jaromir-sukuba/rsyn/media/IMG_20230515_151459656.jpg

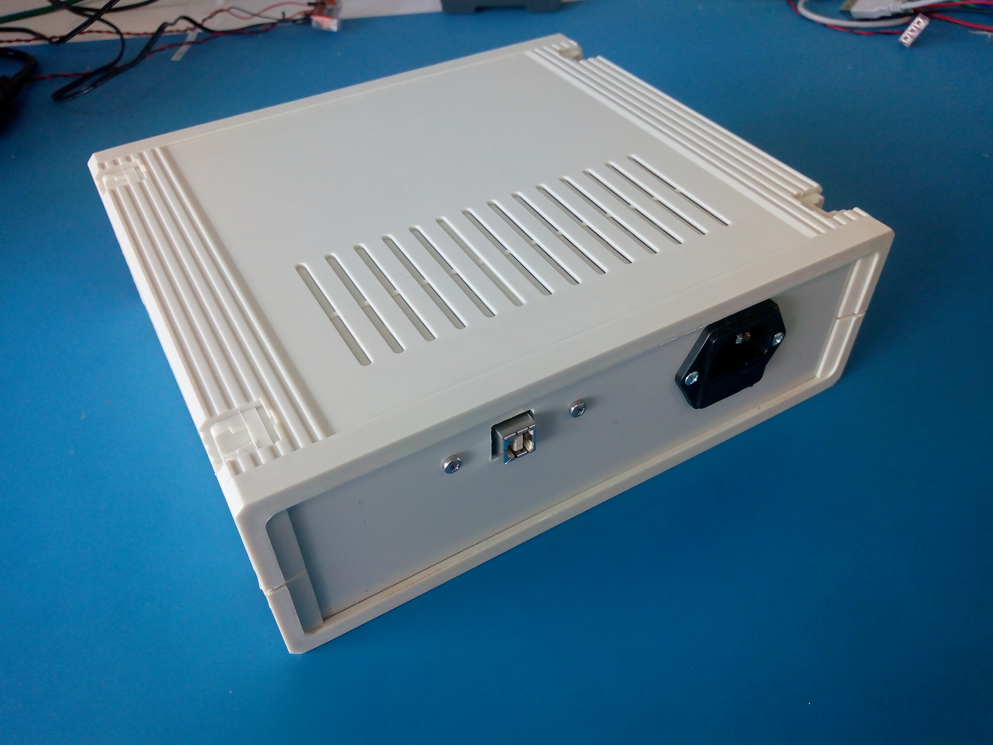
media/IMG_20230515_151459656.jpg
